mrWheel/DSMRlogger32/DSMRlogger32/include/processTelegram.h

#ifndef PROCESSTELEGRAM_H
#define PROCESSTELEGRAM_H

//============ Includes ====================
#include "arduinoGlue.h"

DECLARE_TIMER_EXTERN(publishMQTTtimer);

//============ Added by Convertor ==========
#endif // PROCESSTELEGRAM_H
