mrWheel/DSMRlogger32/DSMRlogger32/src/wifiEvents.cpp

/*
** espressif/arduino-esp32
** https://github.com/espressif/arduino-esp32/blob/master/libraries/WiFi/examples/WiFiClientEvents/WiFiClientEvents.ino
** 
*/
//============ Includes ====================
#include "wifiEvents.h"

//============ Added by Convertor ==========
bool        lostWiFiConnection  = true;
bool        firstConnectionLost = true;
uint32_t    disconnectWiFiStart = 0;
int         lostWiFiCount       = -1;

//----------------------------------------------------------------------------
void WiFiEvent(WiFiEvent_t event)
{
    Debugln();
    DebugTf("[WiFi-event] event: [%d] ", event);

    switch (event) 
    {
        case ARDUINO_EVENT_WIFI_READY: 
            Debugln("WiFi interface ready");
            break;
        case ARDUINO_EVENT_WIFI_SCAN_DONE:
            Debugln("Completed scan for access points");
            break;
        case ARDUINO_EVENT_WIFI_STA_START:
            Debugln("WiFi client started");
            break;
        case ARDUINO_EVENT_WIFI_STA_STOP:
            Debugln("WiFi clients stopped");
            break;
        case ARDUINO_EVENT_WIFI_STA_CONNECTED:
            Debugln("Connected to access point");
            if ((lostWiFiCount % 25) == 0)
            {
              writeToSysLog("Connected to AP successfully!");    
            }                    
            //-- wait for IP address - lostWiFiConnection = false;
            break;
        case ARDUINO_EVENT_WIFI_STA_DISCONNECTED:
            lostWiFiCount++;
            if (disconnectWiFiStart == 0) { disconnectWiFiStart = millis(); }
            if ((lostWiFiCount % 25) == 0)
            {
              Debugln("Disconnected from WiFi access point");
              writeToSysLog("Disconnected from WiFi access point"); 
            }                        
            lostWiFiConnection = true;
            break;
        case ARDUINO_EVENT_WIFI_STA_AUTHMODE_CHANGE:
            Debugln("Authentication mode of access point has changed");
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
